Slamy/fpga-color-pong/gowin/src/gowin_rpll/gowin_rpll_tmp.v

//Copyright (C)2014-2023 Gowin Semiconductor Corporation.
//All rights reserved.
//File Title: Template file for instantiation
//GOWIN Version: V1.9.9 Beta-6
//Part Number: GW1NR-LV9QN88PC6/I5
//Device: GW1NR-9
//Device Version: C
//Created Time: Thu Dec 21 22:49:58 2023

//Change the instance name and port connections to the signal names
//--------Copy here to design--------

    Gowin_rPLL your_instance_name(
        .clkout(clkout_o), //output clkout
        .lock(lock_o), //output lock
        .clkin(clkin_i) //input clkin
    );

//--------Copy end-------------------
